JohnMcLear/NFC-Sweet-Spot-Tester/pictures/IMG_20130802_145224.jpg

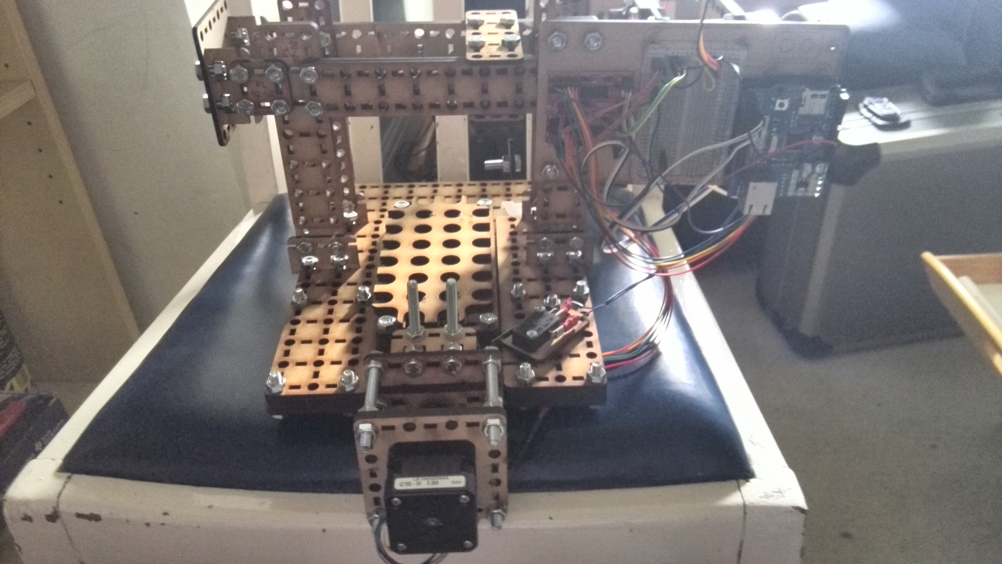
pictures/IMG_20130802_145224.jpg
