JohnMcLear/NFC-Sweet-Spot-Tester/pictures/IMG_20130802_145241.jpg

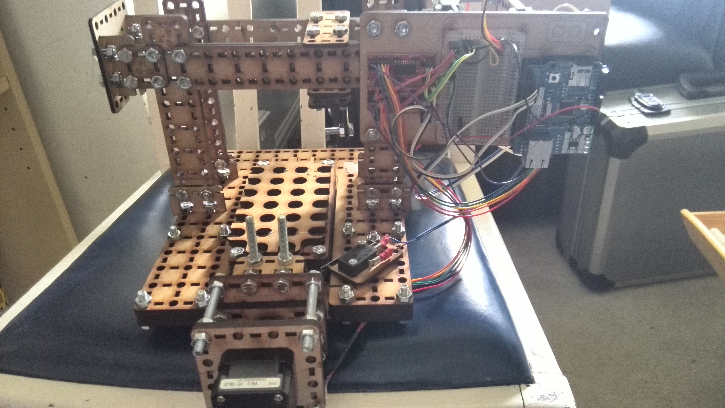
pictures/IMG_20130802_145241.jpg
